ozerik/alm014-fizzle-guts/schematics/FZ-FILTER/FZ-FILTER_1.kicad_sch

## KiCad design schematics/FZ-FILTER/FZ-FILTER_1.kicad_sch (2026-04-29)

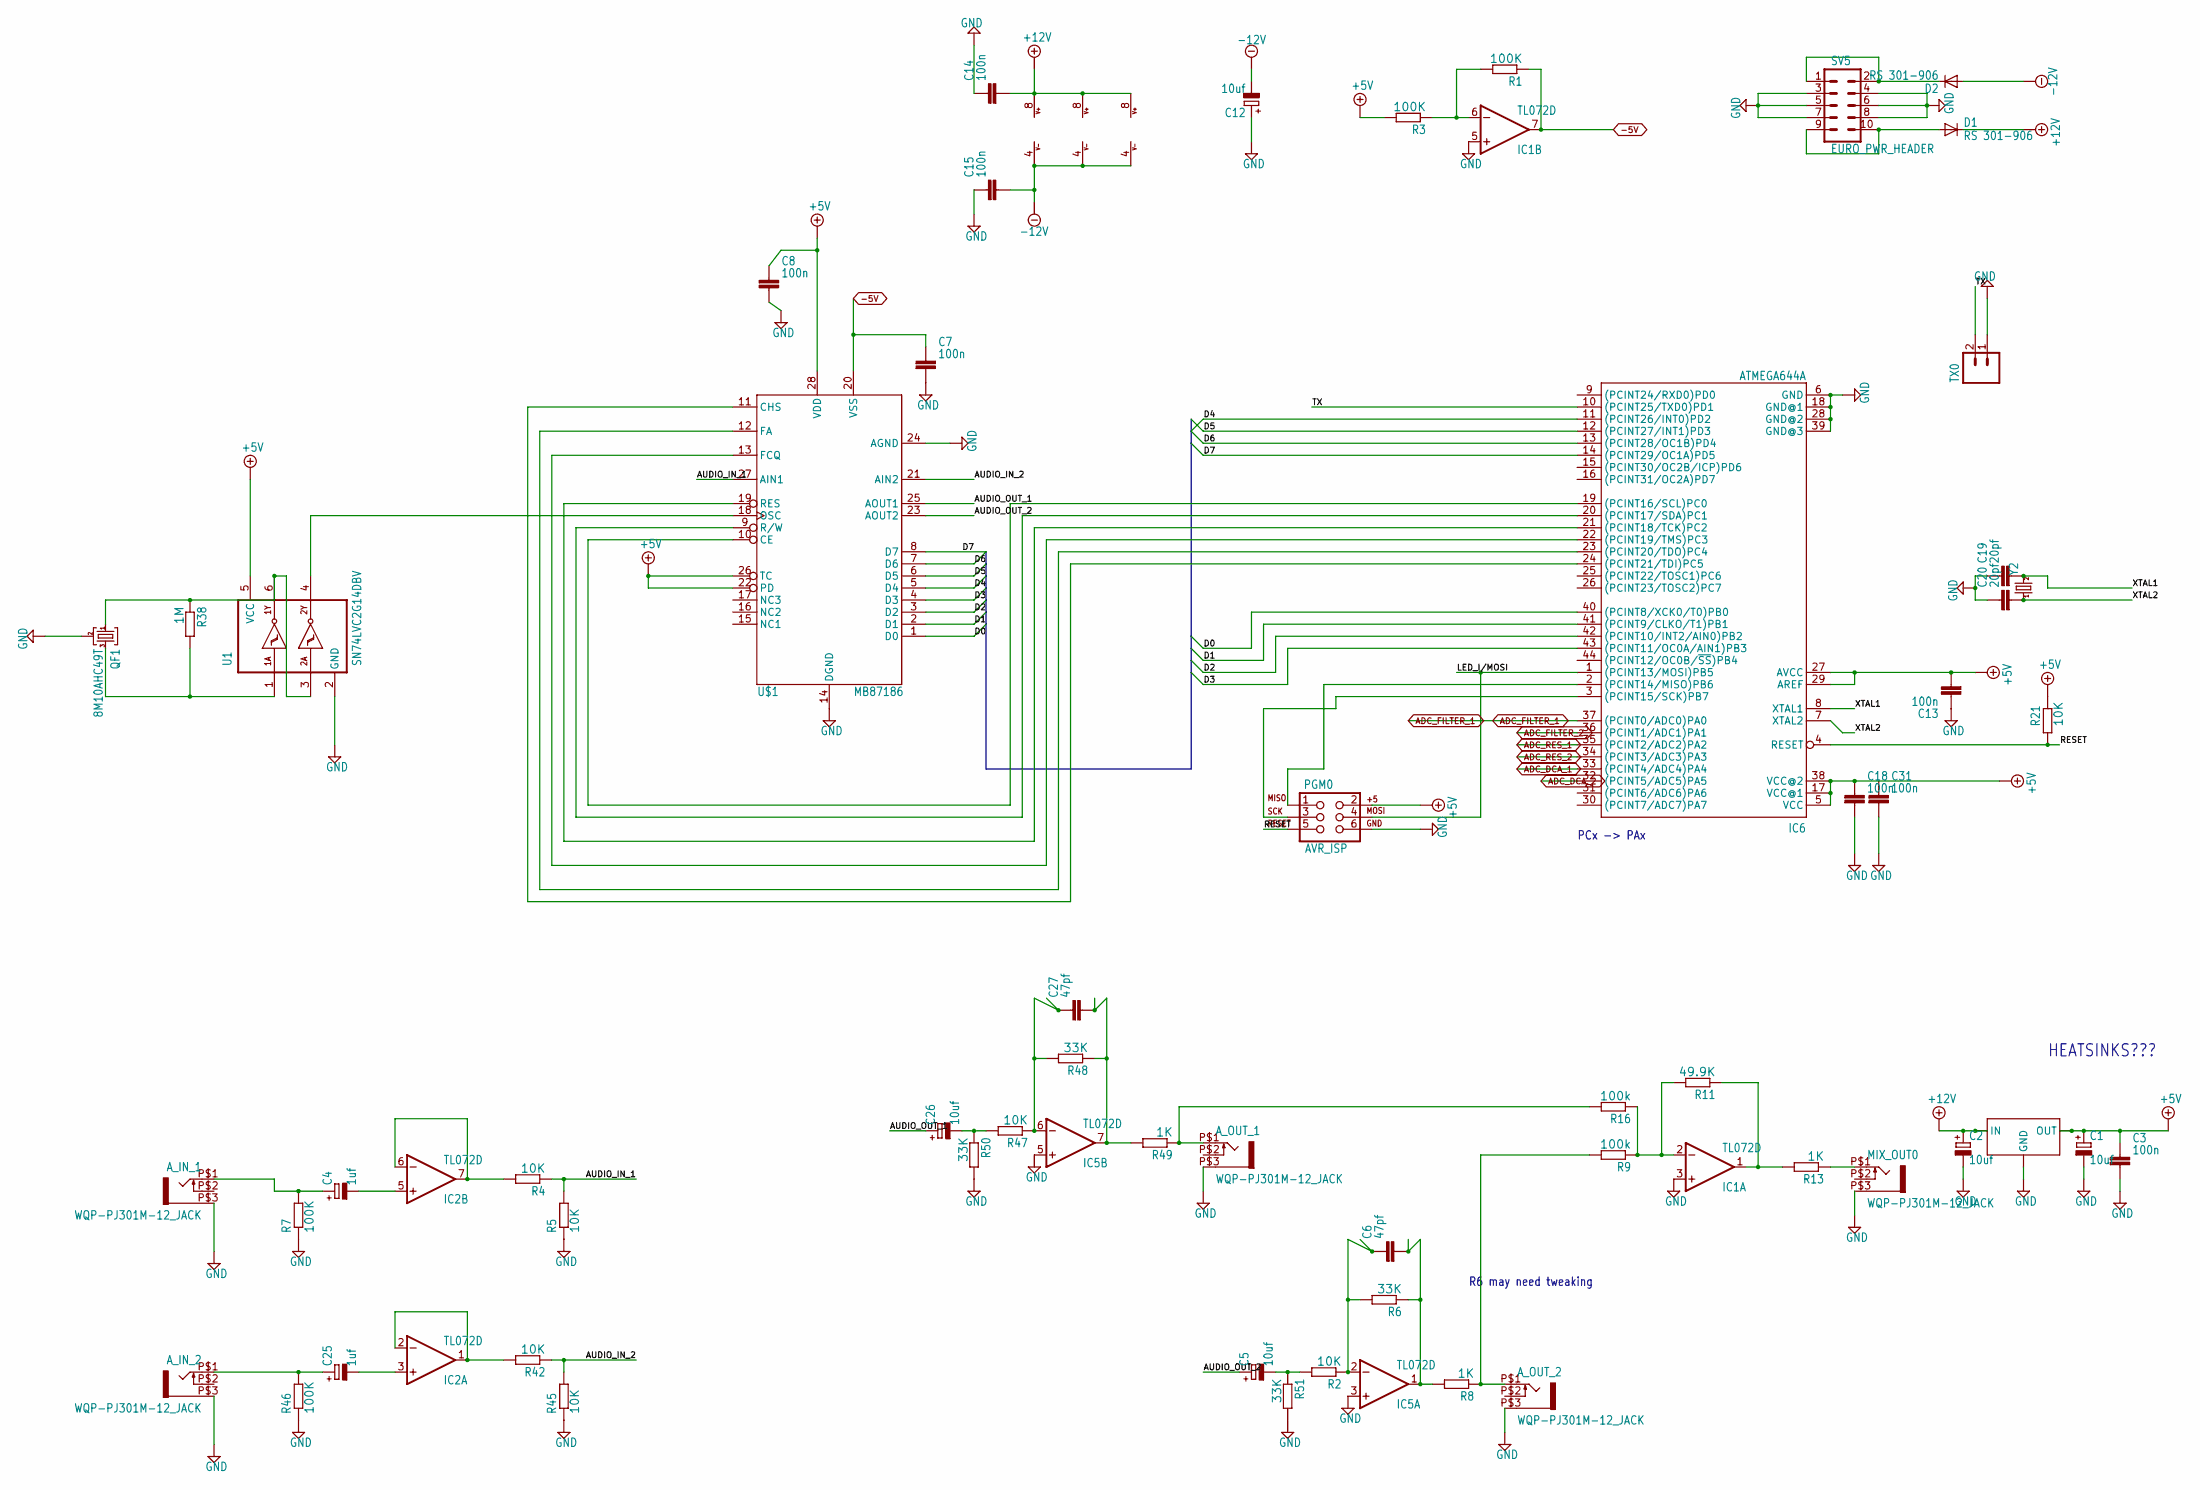
[picture p8: schematic FZ-FILTER_1.kicad_sch]

Parts:
A_IN_1, A_IN_2: WQP-PJ301M-12_JACK
A_OUT_1, A_OUT_2: WQP-PJ301M-12_JACK
C1, C2, C5, C12, C26: 10uf; PANASONIC_B
C3, C7, C8, C13, C14, C15, C18, C31: 100n; C0603
C4, C25: 1uf; PANASONIC_B
C6, C27: 47pf; C0603
C19, C20: 20pf; C0603
D1, D2: RS 301-906; SMB-DIODE
IC1, IC2, IC5: TL072D; SO08
IC6: ATMEGA644A; TQFP44
MIX_OUT0: WQP-PJ301M-12_JACK
PGM0: AVR_ISP; 2X3
QF1: 8M10AHC49T; HC49U
R1, R3, R7, R46: 100K; R0603
R2, R4, R5, R21, R42, R45, R47: 10K; R0603
R6, R48, R50, R51: 33K; R0603
R8, R13, R49: 1K; R0603
R9, R16: 100k; R0603
R11: 49.9K; R0603
R38: 1M; R0603
SV5: EURO_PWR_HEADER
TX0: M02PTH; 1X02
U1: SN74LVC2G14DBV; SOT23-6
U3: 7805; VREG-7805-DPAK2
U$1: MB87186; DIP28
Y2: CRYSTALSMD; HC49UP

Connections:
+5V: C1.+, C3.1, C8.1, C13.2, C18.1, IC6.5 (VCC), IC6.17 (VCC@1), IC6.27 (AVCC), IC6.29 (AREF), IC6.38 (VCC@2), PGM0.2, R3.2, R21.2, U1.5 (VCC), U3.VOUT (OUT), U$1.22 (PD), U$1.26 (TC), U$1.28 (VDD)
+12V: C2.+, C14.2, D1.C, IC1.8 (V+), IC2.8 (V+), IC5.8 (V+), U3.VIN (IN)
-5V: C7.1, IC1.7 (OUT), R1.1, U$1.20 (VSS)
-12V: C12.-, C15.2, D2.A, IC1.4 (V-), IC2.4 (V-), IC5.4 (V-)
ADC_DCA_1: IC6.33 ((PCINT4/ADC4)PA4)
ADC_DCA_2: IC6.32 ((PCINT5/ADC5)PA5)
ADC_FILTER_1: IC6.37 ((PCINT0/ADC0)PA0)
ADC_FILTER_2: IC6.36 ((PCINT1/ADC1)PA1)
ADC_RES_1: IC6.35 ((PCINT2/ADC2)PA2)
ADC_RES_2: IC6.34 ((PCINT3/ADC3)PA3)
AUDIO_IN_1: R4.1, R5.2, U$1.27 (AIN1)
AUDIO_IN_2: R42.1, R45.2, U$1.21 (AIN2)
AUDIO_OUT_1: C26.+, U$1.25 (AOUT1)
AUDIO_OUT_2: C5.+, U$1.23 (AOUT2)
D0: IC6.40 ((PCINT8/XCK0/T0)PB0), U$1.1 (D0)
D1: IC6.41 ((PCINT9/CLKO/T1)PB1), U$1.2 (D1)
D2: IC6.42 ((PCINT10/INT2/AIN0)PB2), U$1.3 (D2)
D3: IC6.43 ((PCINT11/OC0A/AIN1)PB3), U$1.4 (D3)
D4: IC6.11 ((PCINT26/INT0)PD2), U$1.5 (D4)
D5: IC6.12 ((PCINT27/INT1)PD3), U$1.6 (D5)
D6: IC6.13 ((PCINT28/OC1B)PD4), U$1.7 (D6)
D7: IC6.14 ((PCINT29/OC1A)PD5), U$1.8 (D7)
GND: A_IN_1.P$3 (1), A_IN_2.P$3 (1), A_OUT_1.P$3 (1), A_OUT_2.P$3 (1), C1.-, C2.-, C3.2, C7.2, C8.2, C12.+, C13.1, C14.1, C15.1, C18.2, C19.1, C20.1, C31.2, IC1.3 (+IN), IC1.5 (+IN), IC5.3 (+IN), IC5.5 (+IN), IC6.6 (GND), IC6.18 (GND@1), IC6.28 (GND@2), IC6.39 (GND@3), MIX_OUT0.P$3 (1), PGM0.6, QF1.2, R5.1, R7.1, R45.1, R46.1, R50.2, R51.2, SV5.3, SV5.4, SV5.5, SV5.6, SV5.7, SV5.8, TX0.1, U1.2 (GND), U3.GND, U$1.14 (DGND), U$1.24 (AGND)
LED_I/MOSI: IC6.1 ((PCINT13/MOSI)PB5), PGM0.4
unnamed: A_IN_1.P$1 (2), C4.+, R7.2
unnamed: A_IN_2.P$1 (2), C25.+, R46.2
unnamed: A_OUT_1.P$1 (2), R16.2, R49.1
unnamed: A_OUT_2.P$1 (2), R8.1, R9.2
unnamed: C4.-, IC2.5 (+IN)
unnamed: C5.-, R2.2, R51.1
unnamed: C6.1, IC5.2 (-IN), R2.1, R6.2
unnamed: C6.2, IC5.1 (OUT), R6.1, R8.2
unnamed: C25.-, IC2.3 (+IN)
unnamed: C26.-, R47.2, R50.1
unnamed: C27.1, IC5.6 (-IN), R47.1, R48.2
unnamed: C27.2, IC5.7 (OUT), R48.1, R49.2
unnamed: D1.A, SV5.9, SV5.10
unnamed: D2.C, SV5.1, SV5.2
unnamed: IC1.1 (OUT), R11.1, R13.2
unnamed: IC1.2 (-IN), R9.1, R11.2, R16.1
unnamed: IC1.6 (-IN), R1.2, R3.1
unnamed: IC2.1 (OUT), IC2.2 (-IN), R42.2
unnamed: IC2.6 (-IN), IC2.7 (OUT), R4.2
unnamed: IC6.2 ((PCINT14/MISO)PB6), PGM0.1
unnamed: IC6.3 ((PCINT15/SCK)PB7), PGM0.3
unnamed: IC6.19 ((PCINT16/SCL)PC0), U$1.10 (CE)
unnamed: IC6.20 ((PCINT17/SDA)PC1), U$1.9 (R/W)
unnamed: IC6.21 ((PCINT18/TCK)PC2), U$1.19 (RES)
unnamed: IC6.22 ((PCINT19/TMS)PC3), U$1.13 (FCQ)
unnamed: IC6.23 ((PCINT20/TDO)PC4), U$1.12 (FA)
unnamed: IC6.24 ((PCINT21/TDI)PC5), U$1.11 (CHS)
unnamed: MIX_OUT0.P$1 (2), R13.1
unnamed: QF1.1, R38.1, U1.3 (2A), U1.6 (1Y)
unnamed: QF1.3, R38.2, U1.1 (1A)
unnamed: U1.4 (2Y), U$1.18 (OSC)
RESET: IC6.4 (RESET), PGM0.5, R21.1
TX: IC6.10 ((PCINT25/TXD0)PD1), TX0.2
XTAL1: C19.2, IC6.8 (XTAL1), Y2.2
XTAL2: C20.2, IC6.7 (XTAL2), Y2.1

Notes on the sheet:
HEATSINKS???
R6 may need tweaking
PCx -> PAx
