ozerik/alm014-fizzle-guts/schematics/FZ-FILTER/FZ-FILTER_2.kicad_sch

## KiCad design schematics/FZ-FILTER/FZ-FILTER_2.kicad_sch (2026-04-29)

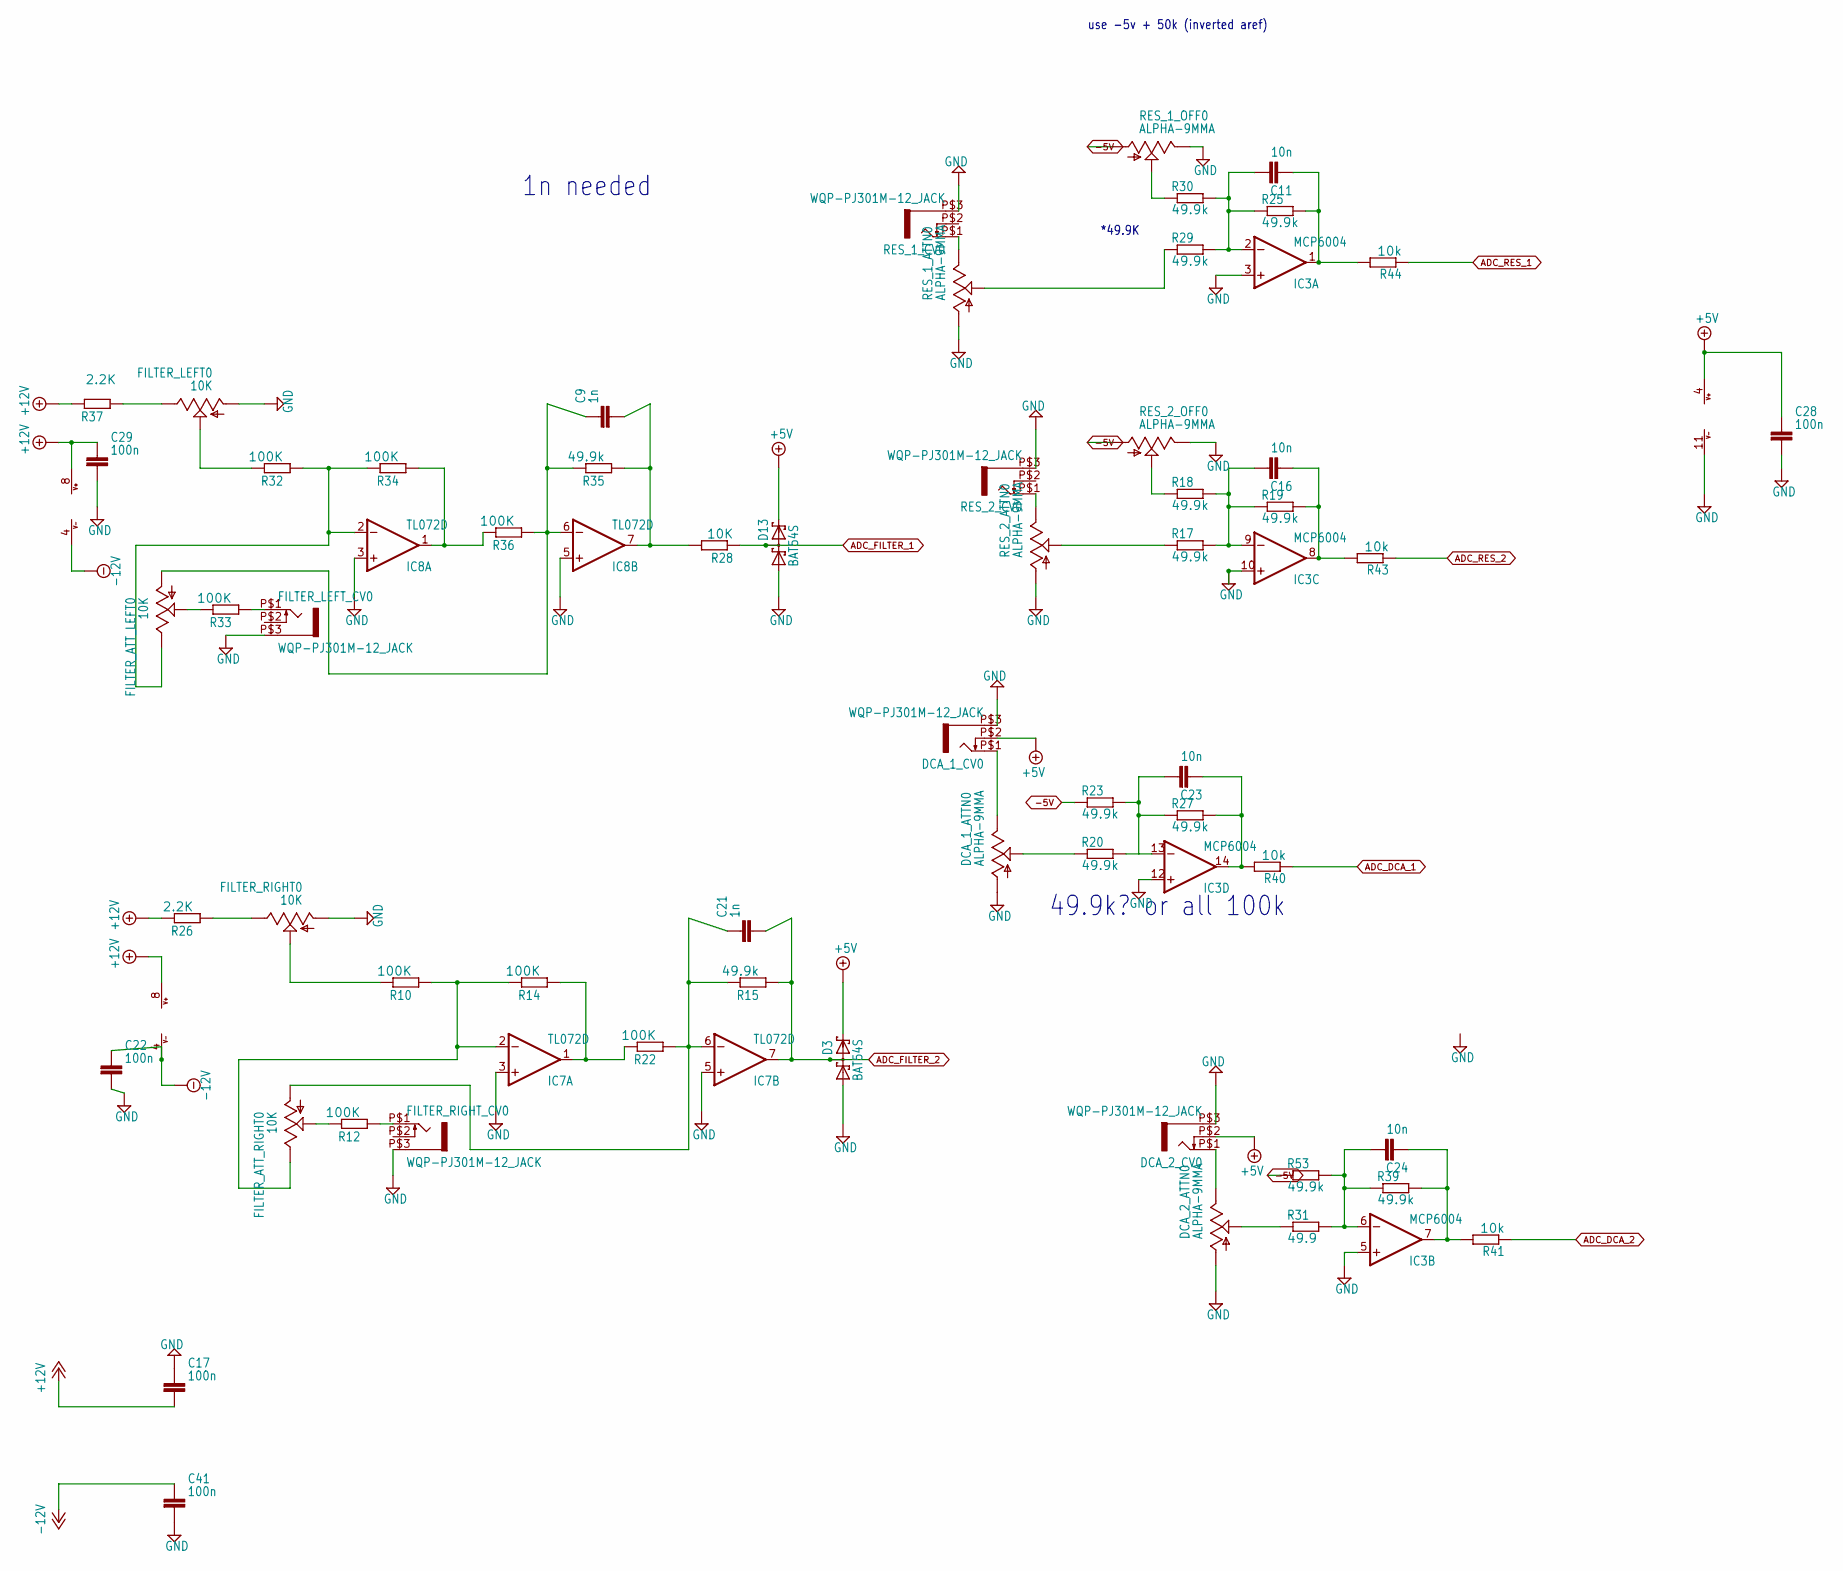
[picture p9: schematic FZ-FILTER_2.kicad_sch]

Parts:
C9, C21: 1n; C0603
C11, C16, C23, C24: 10n; C0603
C17, C22, C28, C29, C41: 100n; C0603
D3, D13: BAT54S; SOT23
DCA_1_ATTN0, DCA_2_ATTN0: ALPHA-9MMA; EVUF
DCA_1_CV0, DCA_2_CV0: WQP-PJ301M-12_JACK
FILTER_ATT_LEFT0: 10K; EVUF
FILTER_ATT_RIGHT0: 10K; EVUF
FILTER_LEFT0: 10K; EVUF
FILTER_LEFT_CV0: WQP-PJ301M-12_JACK
FILTER_RIGHT0: 10K; EVUF
FILTER_RIGHT_CV0: WQP-PJ301M-12_JACK
IC3: MCP6004; SO14
IC7, IC8: TL072D; SO08
R10, R12, R14, R22, R32, R33, R34, R36: 100K; R0603
R15, R17, R18, R19, R20, R23, R25, R27, R29, R30, R35, R39, R53: 49.9k; R0603
R26, R37: 2.2K; R0603
R28: 10K; R0603
R31: 49.9; R0603
R40, R41, R43, R44: 10k; R0603
RES_1_ATTN0, RES_1_OFF0, RES_2_ATTN0, RES_2_OFF0: ALPHA-9MMA; EVUF
RES_1_CV0, RES_2_CV0: WQP-PJ301M-12_JACK

Connections:
+5V: C28.1, D3.2 (C2), D13.2 (C2), DCA_1_CV0.P$2 (3), DCA_2_CV0.P$2 (3), IC3.4 (V+)
+12V: C17.2, C29.1, IC7.8 (V+), IC8.8 (V+), R26.2, R37.2
-5V: R23.1, R53.1, RES_1_OFF0.1 (A), RES_2_OFF0.1 (A)
-12V: C22.1, C41.1, IC7.4 (V-), IC8.4 (V-)
ADC_DCA_1: R40.1
ADC_DCA_2: R41.1
ADC_FILTER_1: D13.3 (C1A2), R28.1
ADC_FILTER_2: C21.2, D3.3 (C1A2), IC7.7 (OUT), R15.1
ADC_RES_1: R44.1
ADC_RES_2: R43.1
GND: C17.1, C22.2, C28.2, C29.2, C41.2, D3.1 (A1), D13.1 (A1), DCA_1_ATTN0.1 (A), DCA_1_CV0.P$3 (1), DCA_2_ATTN0.1 (A), DCA_2_CV0.P$3 (1), FILTER_LEFT0.1 (A), FILTER_LEFT_CV0.P$3 (1), FILTER_RIGHT0.1 (A), FILTER_RIGHT_CV0.P$3 (1), IC3.3 (+IN), IC3.5 (+IN), IC3.10 (+IN), IC3.11 (V-), IC3.12 (+IN), IC7.3 (+IN), IC7.5 (+IN), IC8.3 (+IN), IC8.5 (+IN), RES_1_ATTN0.1 (A), RES_1_CV0.P$3 (1), RES_1_OFF0.3 (E), RES_2_ATTN0.1 (A), RES_2_CV0.P$3 (1), RES_2_OFF0.3 (E)
unnamed: C9.1, FILTER_ATT_LEFT0.1 (A), IC8.6 (-IN), R35.2, R36.1
unnamed: C9.2, IC8.7 (OUT), R28.2, R35.1
unnamed: C11.1, IC3.2 (-IN), R25.1, R29.2, R30.2
unnamed: C11.2, IC3.1 (OUT), R25.2, R44.2
unnamed: C16.1, IC3.9 (-IN), R17.2, R18.2, R19.1
unnamed: C16.2, IC3.8 (OUT), R19.2, R43.2
unnamed: C21.1, FILTER_ATT_RIGHT0.1 (A), IC7.6 (-IN), R15.2, R22.1
unnamed: C23.1, R23.2, R27.1
unnamed: C23.2, IC3.14 (OUT), R27.2, R40.2
unnamed: C24.1, IC3.6 (-IN), R31.2, R39.1, R53.2
unnamed: C24.2, IC3.7 (OUT), R39.2, R41.2
unnamed: DCA_1_ATTN0.2 (S), R20.1
unnamed: DCA_1_ATTN0.3 (E), DCA_1_CV0.P$1 (2)
unnamed: DCA_2_ATTN0.2 (S), R31.1
unnamed: DCA_2_ATTN0.3 (E), DCA_2_CV0.P$1 (2)
unnamed: FILTER_ATT_LEFT0.2 (S), R33.2
unnamed: FILTER_ATT_LEFT0.3 (E), IC8.2 (-IN), R32.1, R34.2
unnamed: FILTER_ATT_RIGHT0.2 (S), R12.2
unnamed: FILTER_ATT_RIGHT0.3 (E), IC7.2 (-IN), R10.1, R14.2
unnamed: FILTER_LEFT0.2 (S), R32.2
unnamed: FILTER_LEFT0.3 (E), R37.1
unnamed: FILTER_LEFT_CV0.P$1 (2), R33.1
unnamed: FILTER_RIGHT0.2 (S), R10.2
unnamed: FILTER_RIGHT0.3 (E), R26.1
unnamed: FILTER_RIGHT_CV0.P$1 (2), R12.1
unnamed: IC3.13 (-IN), R20.2
unnamed: IC7.1 (OUT), R14.1, R22.2
unnamed: IC8.1 (OUT), R34.1, R36.2
unnamed: R17.1, RES_2_ATTN0.2 (S)
unnamed: R18.1, RES_2_OFF0.2 (S)
unnamed: R29.1, RES_1_ATTN0.2 (S)
unnamed: R30.1, RES_1_OFF0.2 (S)
unnamed: RES_1_ATTN0.3 (E), RES_1_CV0.P$1 (2)
unnamed: RES_2_ATTN0.3 (E), RES_2_CV0.P$1 (2)

Notes on the sheet:
49.9k? or all 100k
*49.9K
1n needed
use -5v + 50k (inverted aref)
